Kavyansh-kohar/SMART-DESK-CONSOLE/project images/20260102_153730.jpg

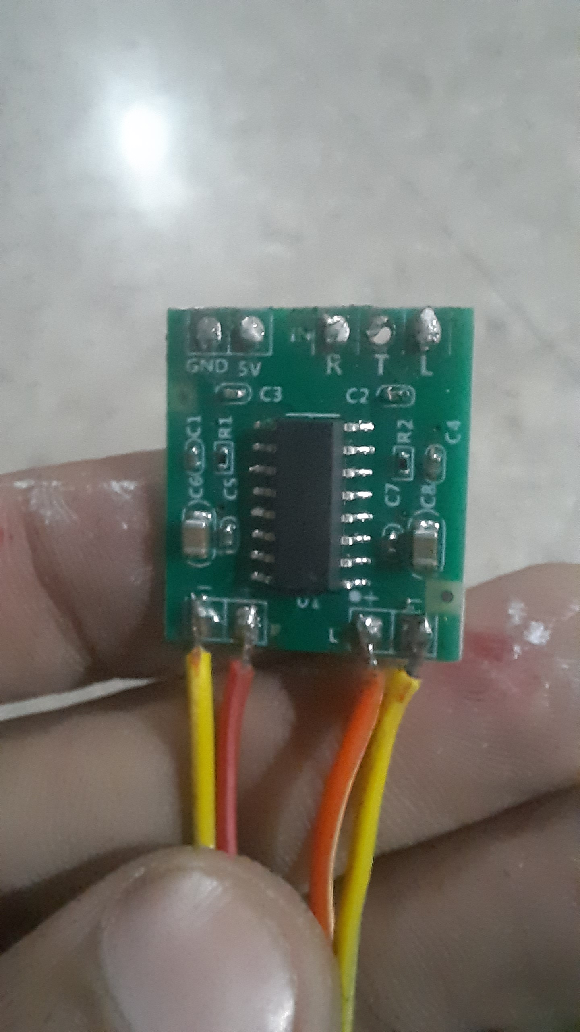
project images/20260102_153730.jpg
