Kavyansh-kohar/SMART-DESK-CONSOLE/project images/20260103_142641.jpg

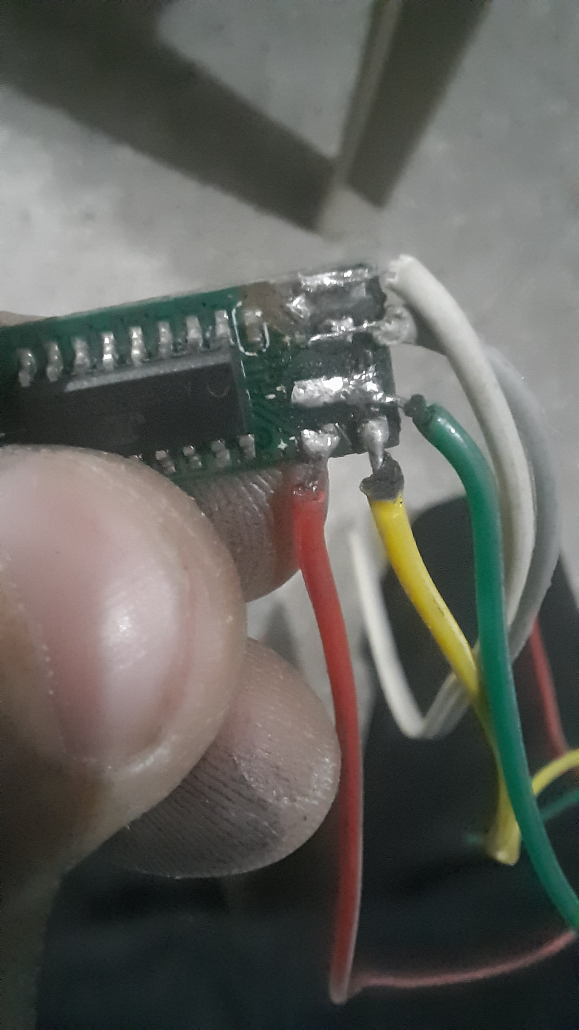
project images/20260103_142641.jpg
