Kavyansh-kohar/SMART-DESK-CONSOLE/project images/20260114_100647.jpg

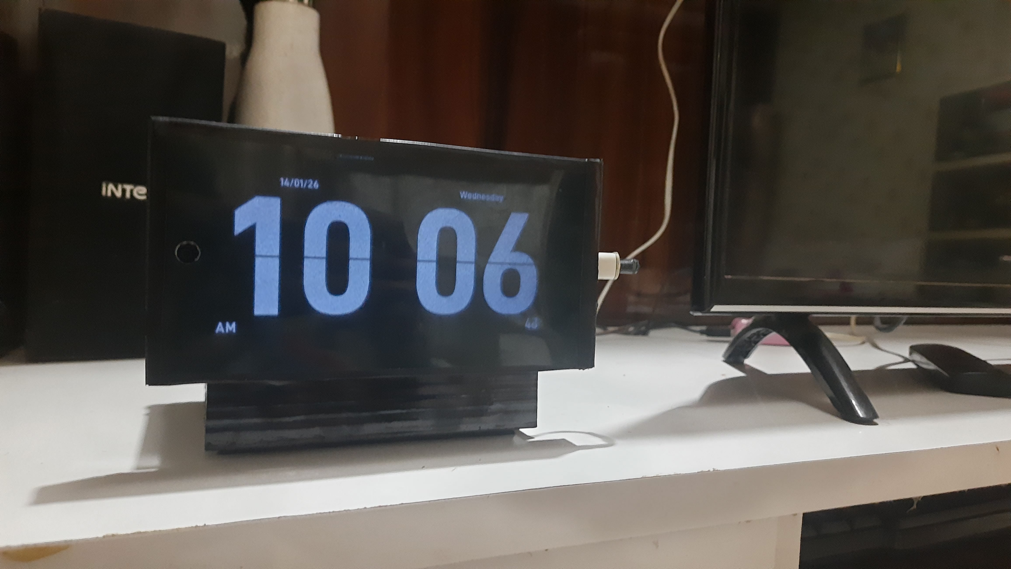
project images/20260114_100647.jpg
