Kavyansh-kohar/SMART-DESK-CONSOLE/project images/20260114_100653.jpg

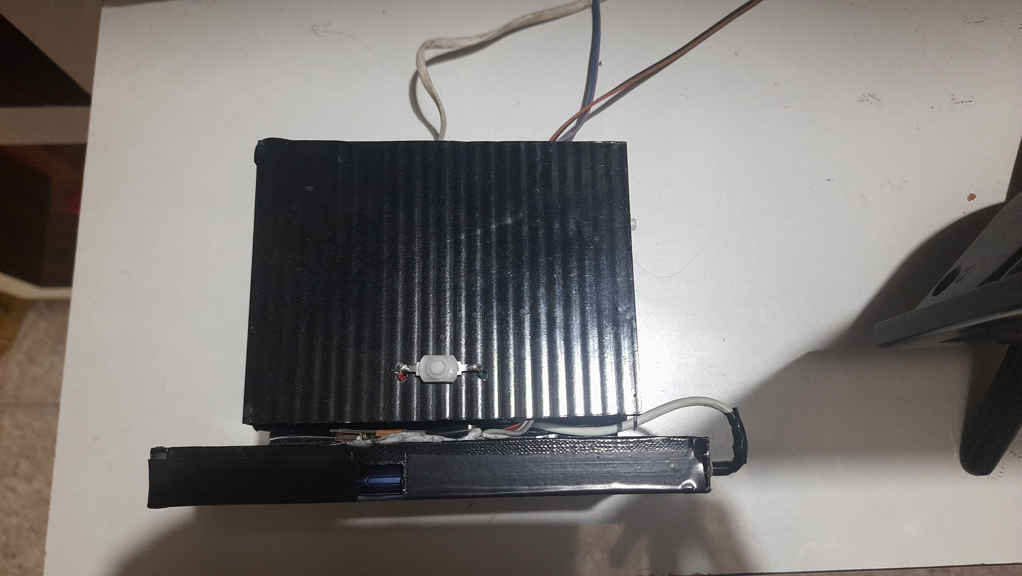
project images/20260114_100653.jpg
