Kavyansh-kohar/SMART-DESK-CONSOLE/project images/20260114_100724.jpg

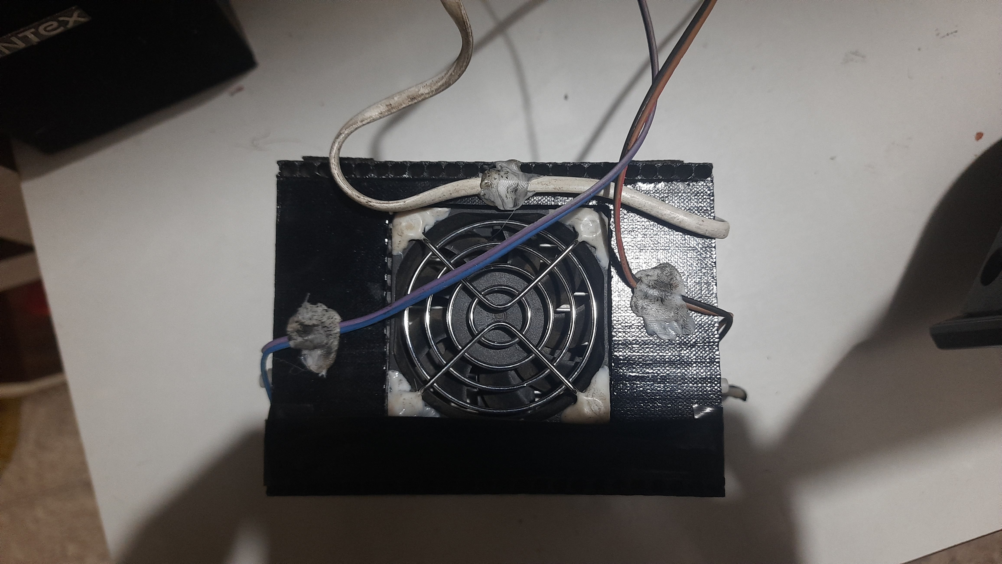
project images/20260114_100724.jpg
