Kavyansh-kohar/SMART-DESK-CONSOLE/project images/image-1767355005560.jpg

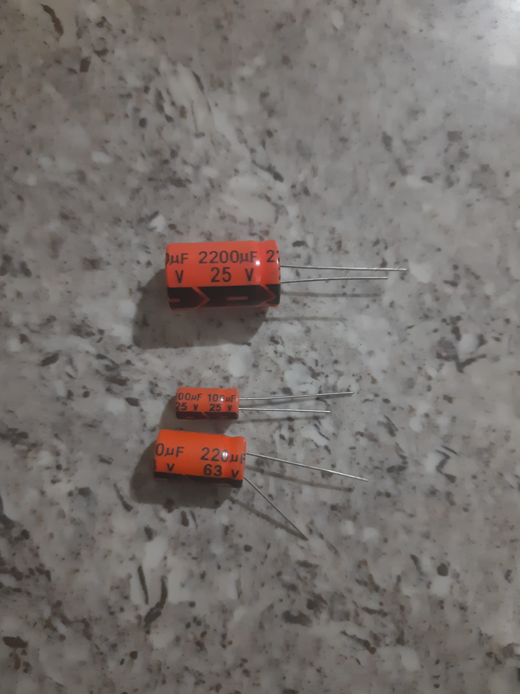
project images/image-1767355005560.jpg
