Kavyansh-kohar/SMART-DESK-CONSOLE/project images/image-1767450404315.jpg

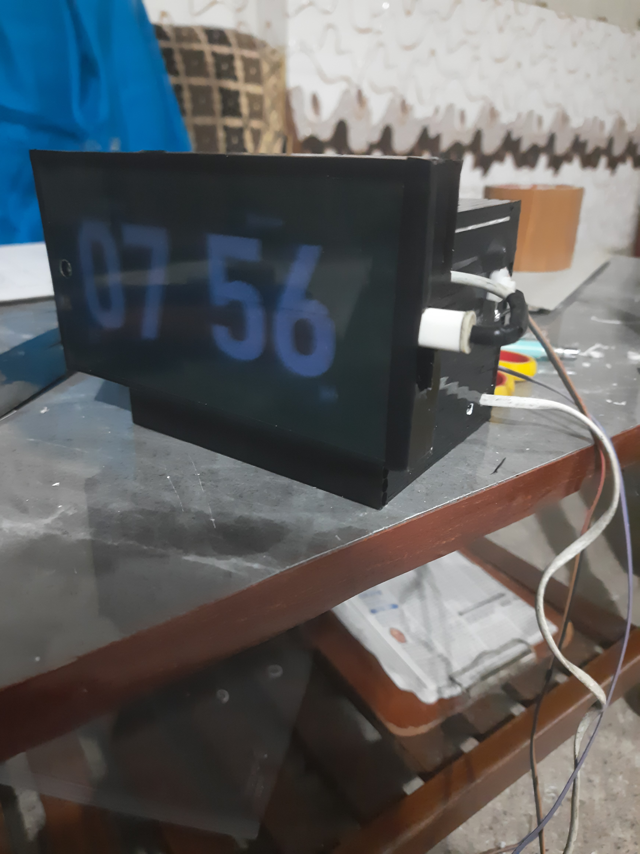
project images/image-1767450404315.jpg
